tvixen/diy-BMS-with-Arduino-Nano/BMS_with_Nano-Circuit/Version 3.0.3/BMS with Nano 3.0.3 brd.pdf

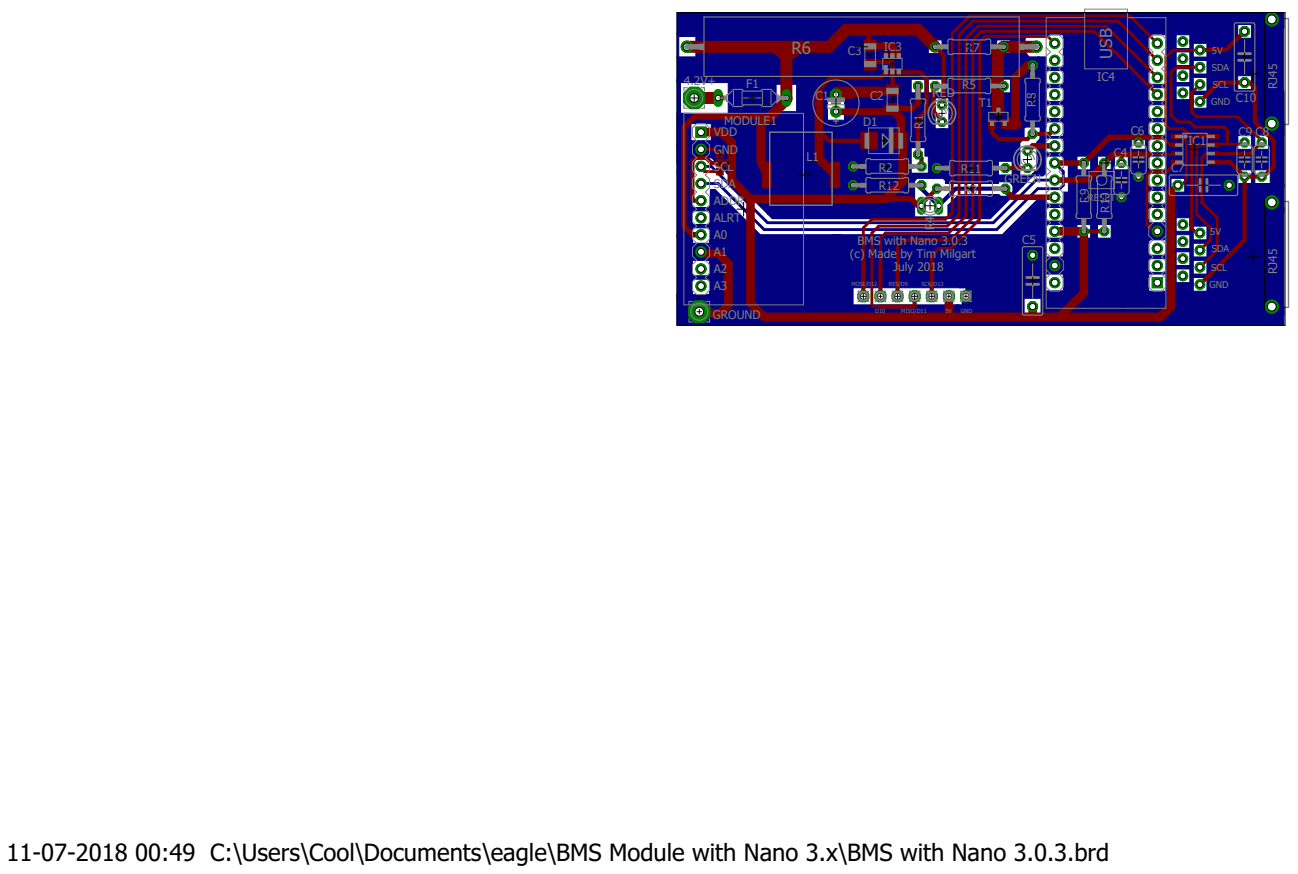
[picture p12: page 1]

F1 | R5 | SCL

VDD
GND

11-07-2018 00:49 C:\Users\Cool\Documents\eagle\BMS Module with Nano 3.x\BMS with Nano 3.0.3.brd
