tvixen/diy-BMS-with-Arduino-Nano/BMS_with_Nano-Circuit/Version 3.0.3/BMS with Nano 3.0.3 sch.pdf

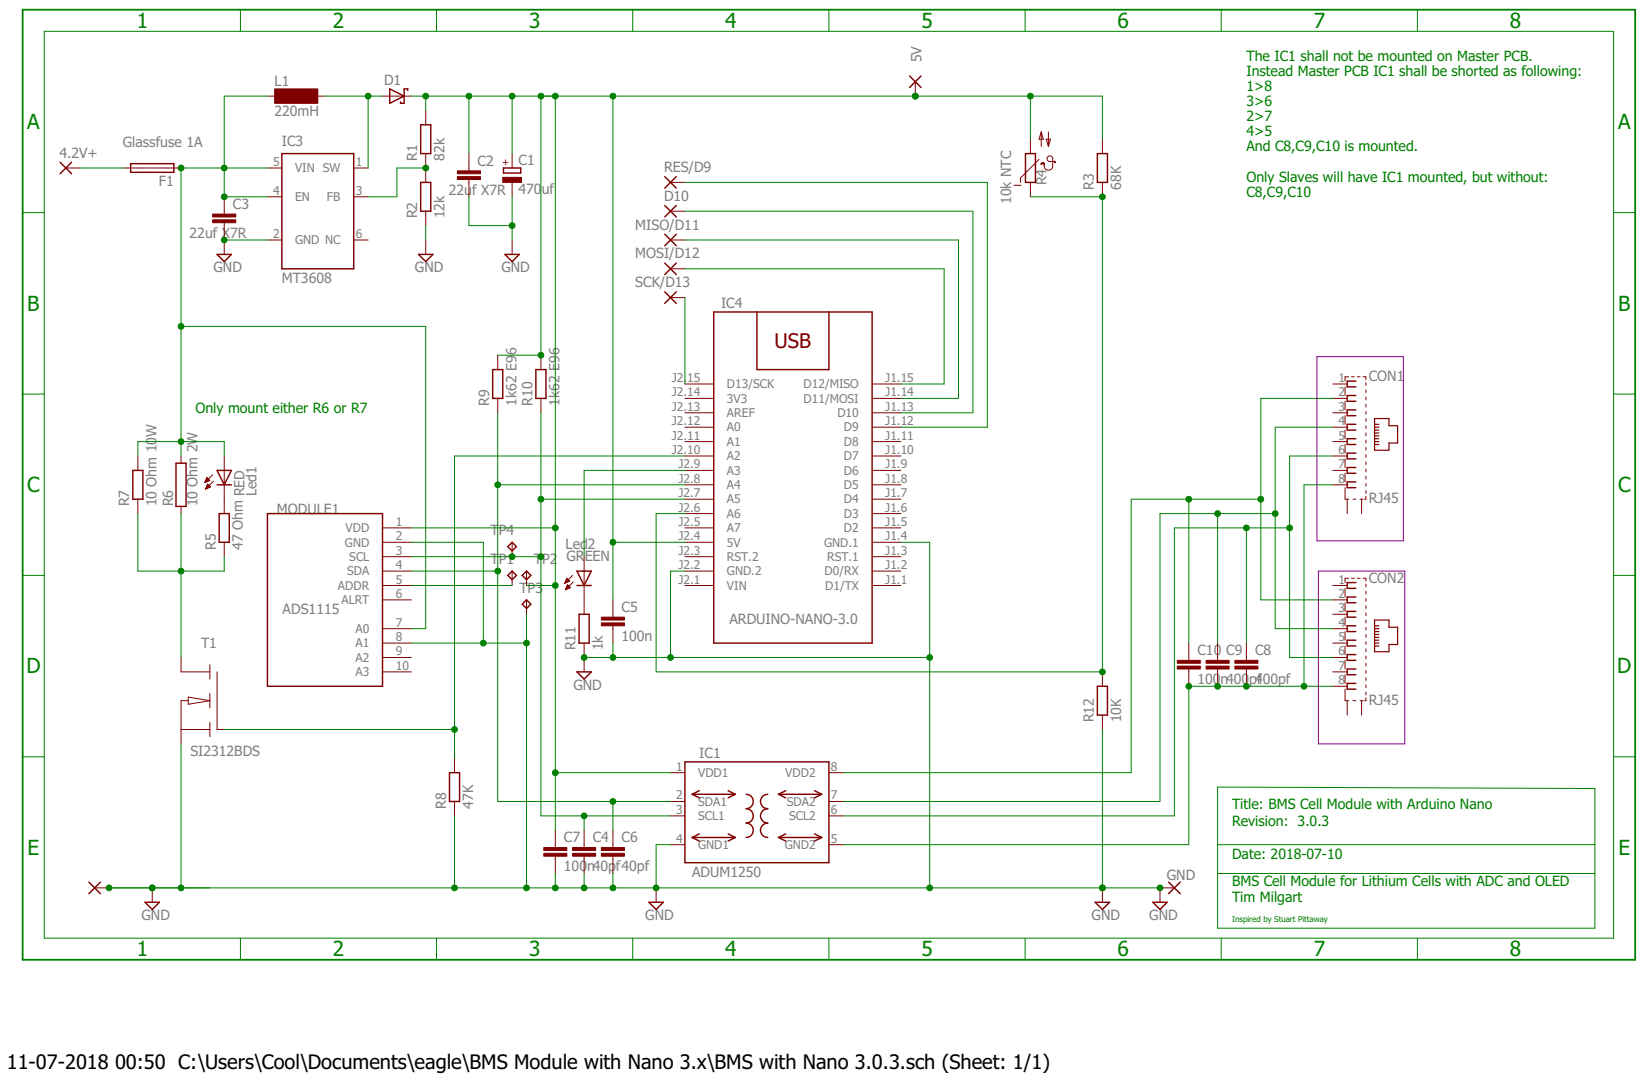
[picture p13: page 1]

The IC1 shall not be mounted on Master PCB. Instead Master PCB IC1 shall be shorted as following: 1>8

And C8,C9,C10 is mounted. Only Slaves will have IC1 mounted, but without: C8,C9,C10

Only mount either R6 or R7

Title: BMS Cell Module with Arduino Nano Revision: 3.0.3

BMS Cell Module for Lithium Cells with ADC and OLED
Tim Milgart

Inspired by Stuart Pittaway

11-07-2018 00:50 C:\Users\Cool\Documents\eagle\BMS Module with Nano 3.x\BMS with Nano 3.0.3.sch (Sheet: 1/1)
