tvixen/diy-BMS-with-Arduino-Nano/BMS_with_Nano-Circuit/Version 3.0.4/Processor for balancer with Nano 3.0.4 sch.pdf

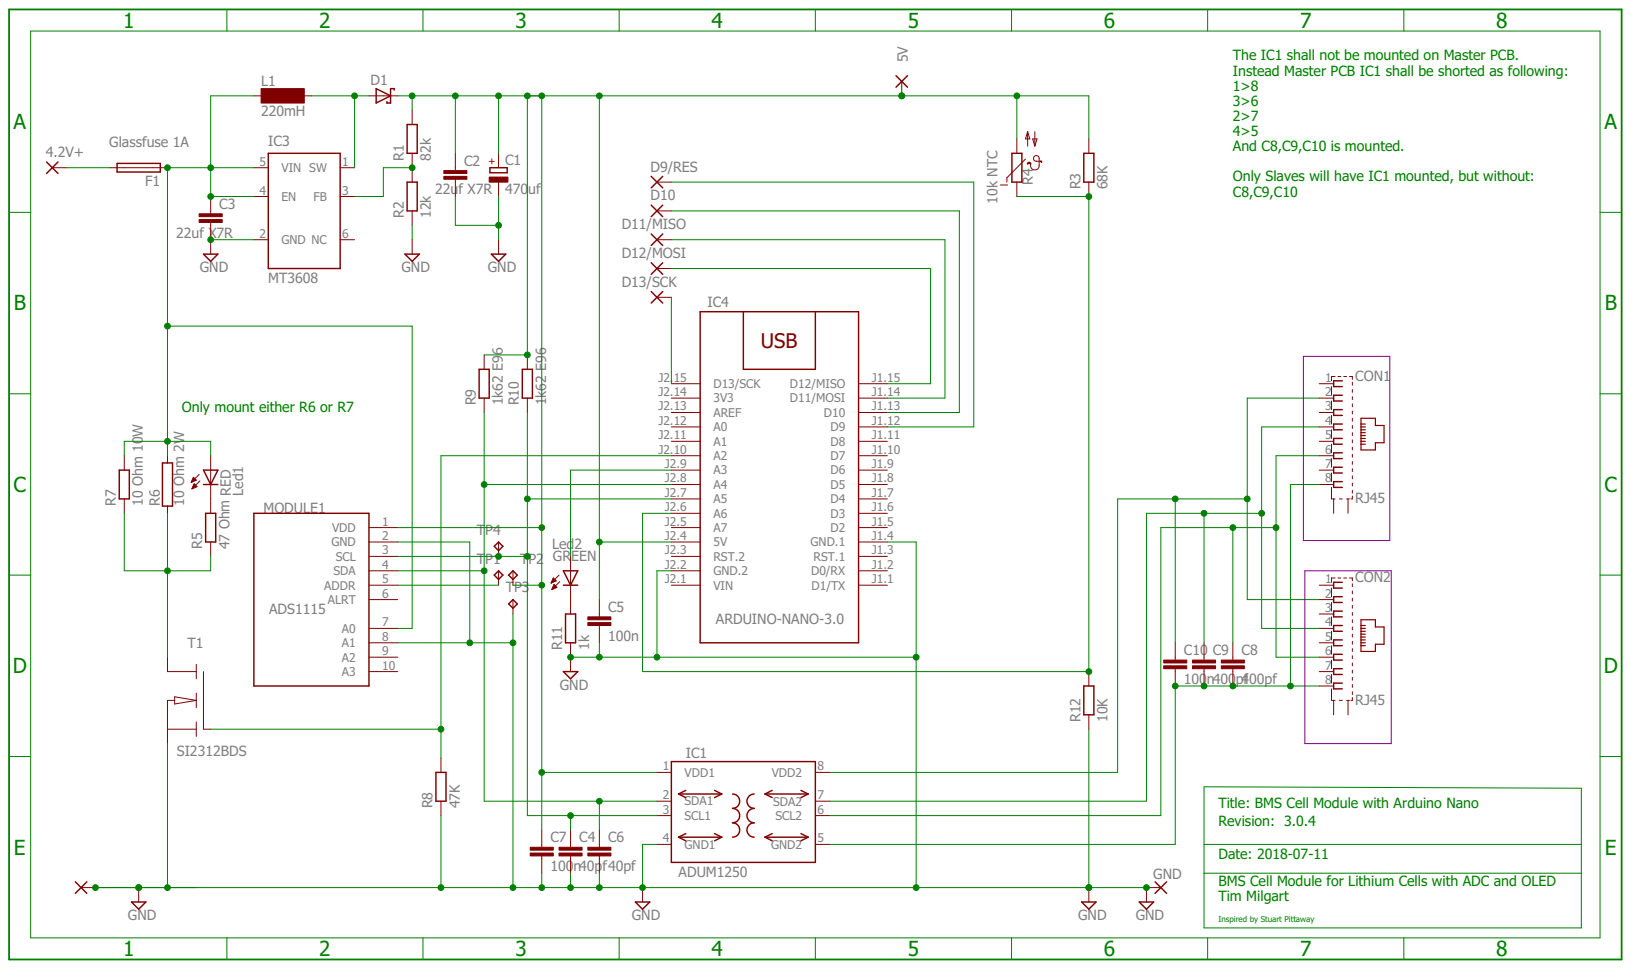
[picture p20: page 1]
